aspro648/RPB/Board/3D/1655.step

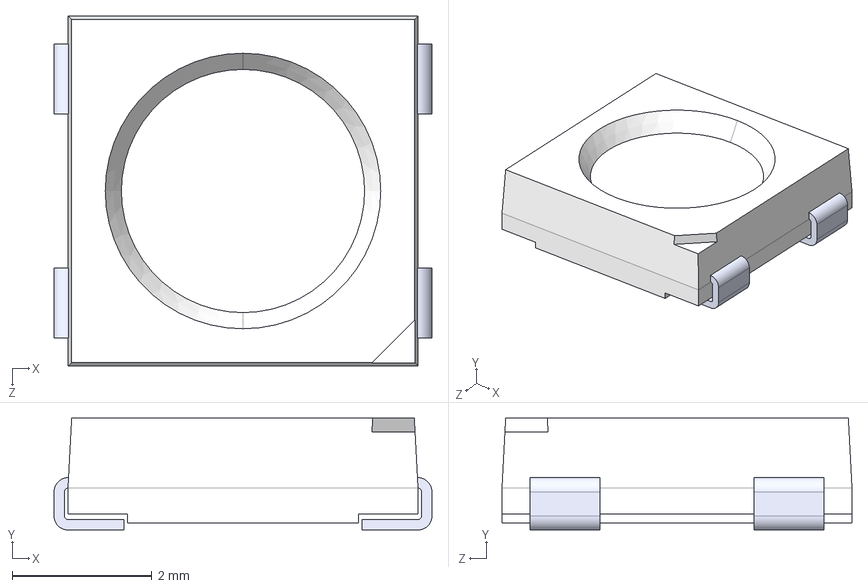
[picture p26: CAD file, 2022-11-20]
Board/3D/1655.step
5.40 x 1.60 x 5.00 mm
