aspro648/RPB/Card 125mm/3D/530471010.stp

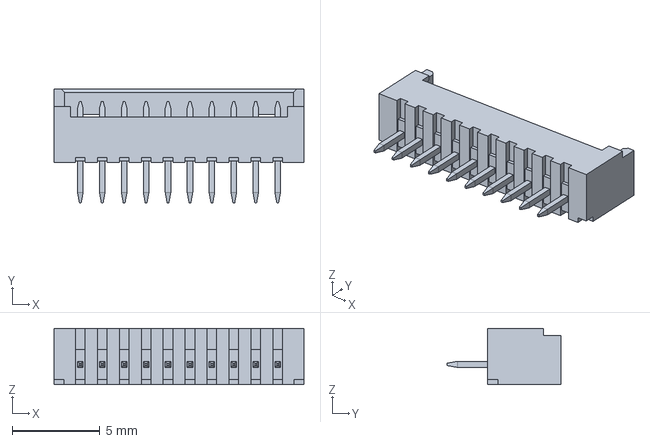
[picture p27: CAD file, 2022-12-04]
Card 125mm/3D/530471010.stp
14.2 x 6.50 x 3.20 mm
