aspro648/RPB/Card ISP/3D/61200621621_Download_STP_61200621621_rev1.stp

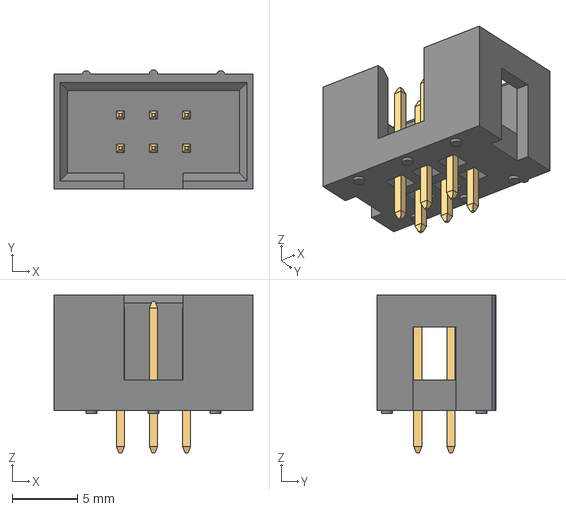
[picture p28: CAD file, 2022-12-04]
Card ISP/3D/61200621621_Download_STP_61200621621_rev1.stp
15.3 x 9.18 x 12.1 mm
6120xx21621_PIN x 6
